dhunink/SaltScale/cad/exports/experimental/step/concept_v4_locator_fit_0p4_v1.step

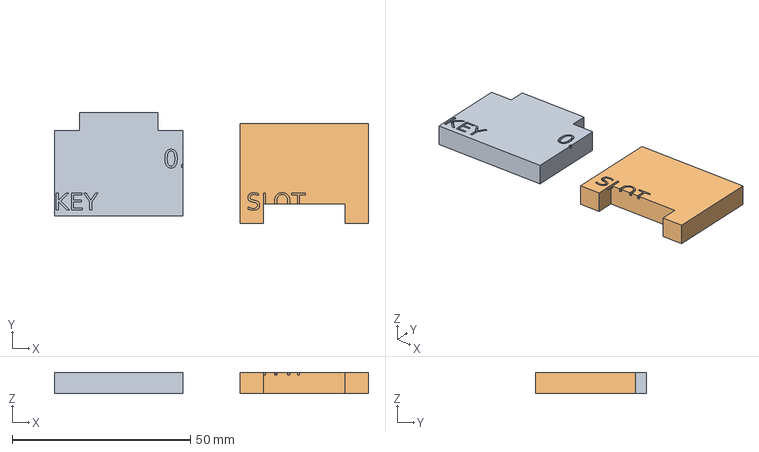
[picture p15: CAD file, 2026-06-13]
cad/exports/experimental/step/concept_v4_locator_fit_0p4_v1.step
88.0 x 31.0 x 6.00 mm
