dhunink/SaltScale/cad/exports/concept_v5_cartridge/step/concept_v5_round_load_puck.step

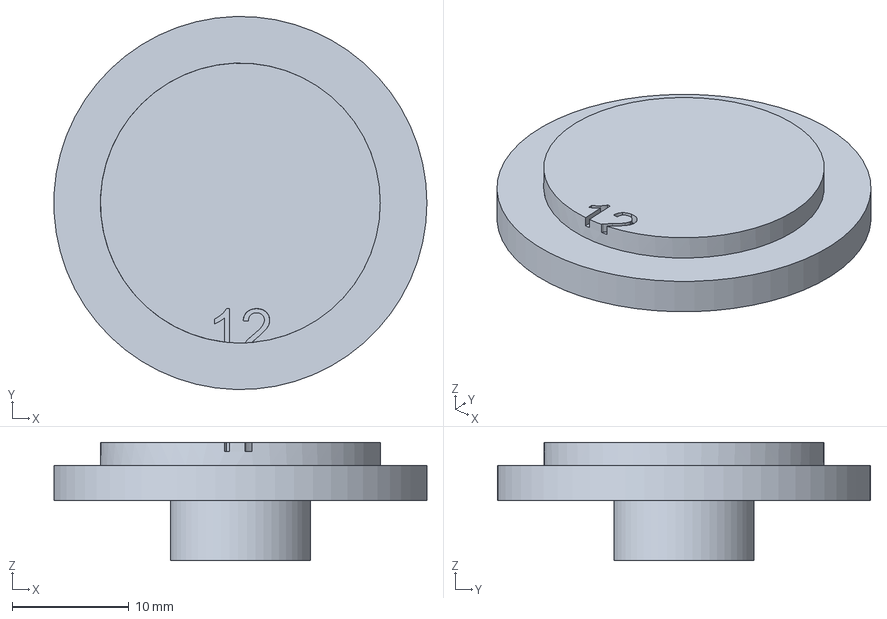
[picture p16: CAD file, 2026-06-15]
cad/exports/concept_v5_cartridge/step/concept_v5_round_load_puck.step
32.0 x 32.0 x 10.2 mm
