dhunink/SaltScale/cad/exports/experimental/step/concept_v4_lower_support_test_v1.step

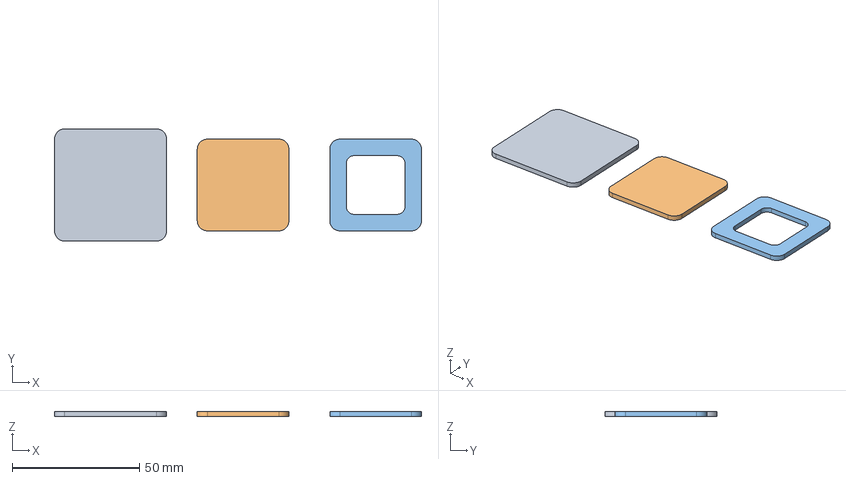
[picture p17: CAD file, 2026-06-13]
cad/exports/experimental/step/concept_v4_lower_support_test_v1.step
144.0 x 44.0 x 2.00 mm
