dhunink/SaltScale/cad/exports/rejected/step/concept_v4_upper_pad_carrier_pocket_test_v1.step

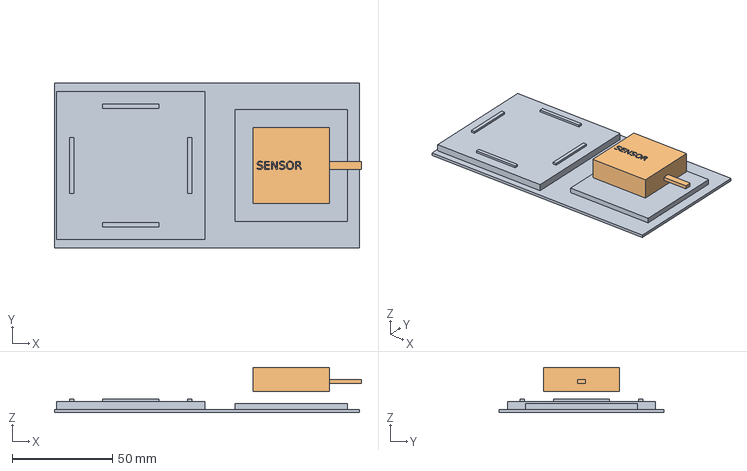
[picture p18: CAD file, 2026-06-13]
cad/exports/rejected/step/concept_v4_upper_pad_carrier_pocket_test_v1.step
153.0 x 82.0 x 22.6 mm
