dhunink/SaltScale/cad/exports/validated/step/concept_v4_upper_pad_pocket_round_cup_v1.step

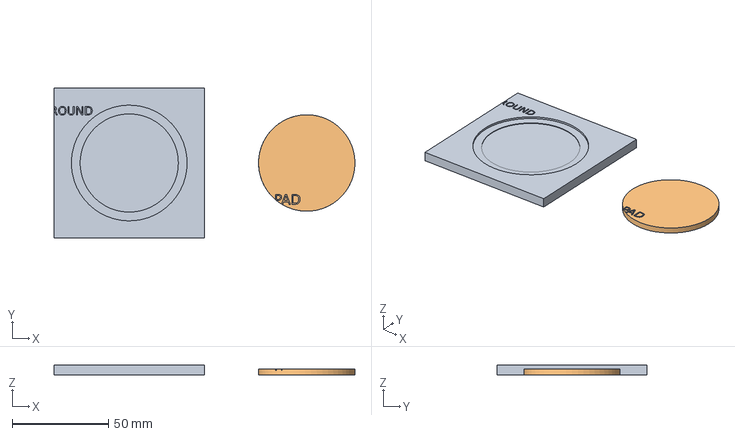
[picture p19: CAD file, 2026-06-13]
cad/exports/validated/step/concept_v4_upper_pad_pocket_round_cup_v1.step
156.0 x 78.0 x 5.00 mm
