dhunink/SaltScale/cad/exports/active/step/concept_v4_lower_pad.step

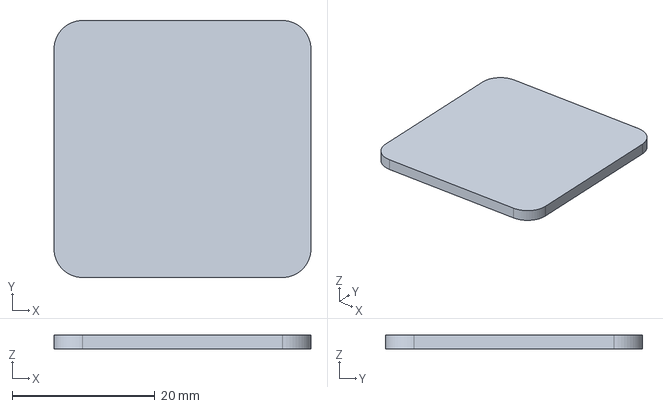
[picture p20: CAD file, 2026-06-13]
cad/exports/active/step/concept_v4_lower_pad.step
36.0 x 36.0 x 2.00 mm
