dhunink/SaltScale/cad/exports/concept_v5_cartridge/step/concept_v5_upper_segment_0.step

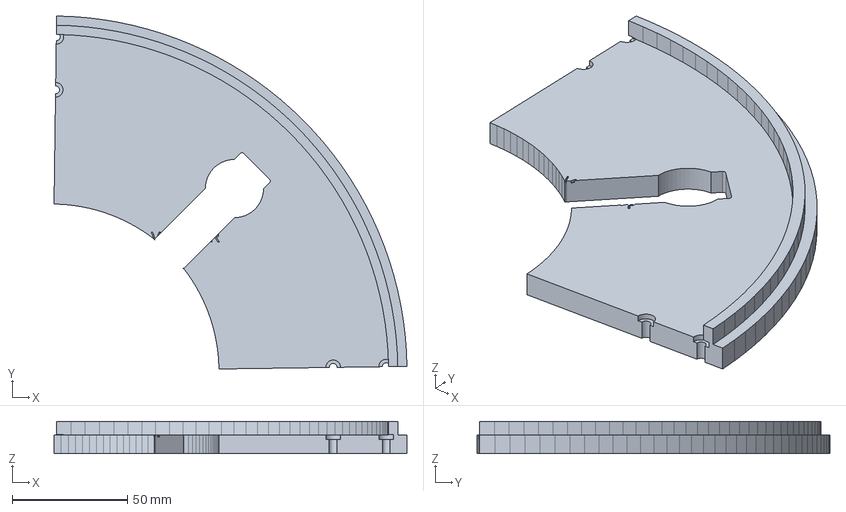
[picture p21: CAD file, 2026-06-15]
cad/exports/concept_v5_cartridge/step/concept_v5_upper_segment_0.step
153.0 x 153.0 x 14.0 mm
