dhunink/SaltScale/cad/exports/rejected/step/concept_v4_upper_pad_sensor_relative_test_v1.step

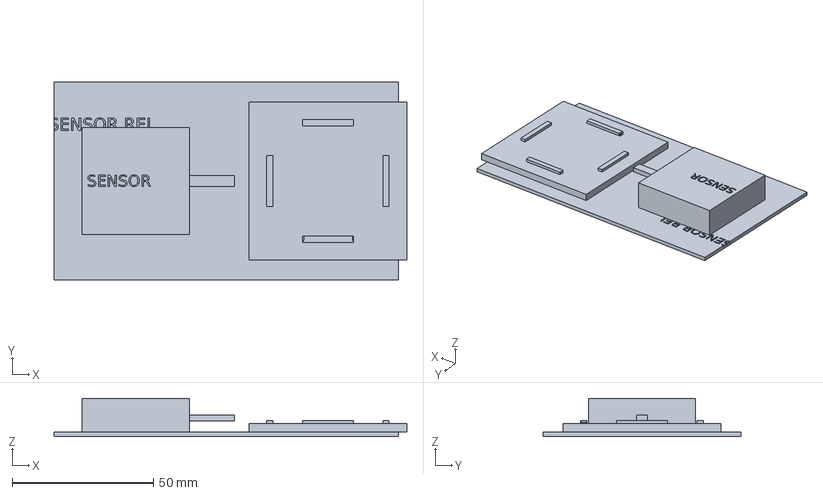
[picture p22: CAD file, 2026-06-13]
cad/exports/rejected/step/concept_v4_upper_pad_sensor_relative_test_v1.step
125.0 x 70.0 x 13.6 mm
