dhunink/SaltScale/cad/exports/active/step/concept_v4_sensor_placeholder.step

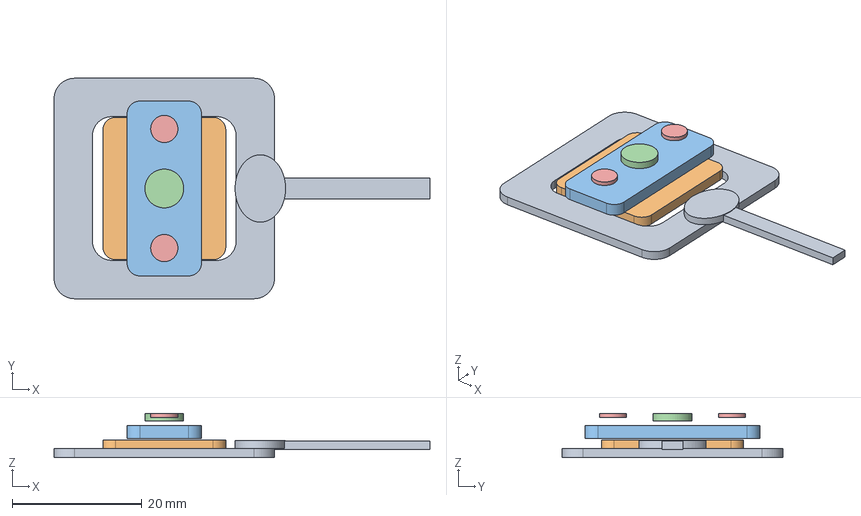
[picture p23: CAD file, 2026-06-13]
cad/exports/active/step/concept_v4_sensor_placeholder.step
58.1 x 34.1 x 6.84 mm
