dhunink/SaltScale/cad/exports/concept_v5_cartridge/step/concept_v5_lower_segment_0.step

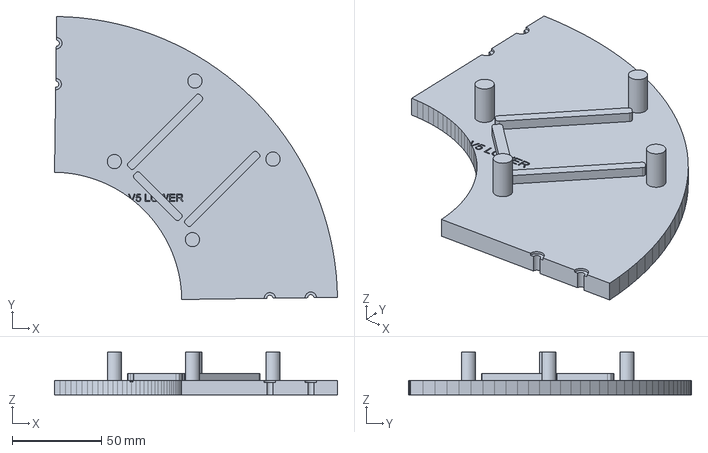
[picture p26: CAD file, 2026-06-15]
cad/exports/concept_v5_cartridge/step/concept_v5_lower_segment_0.step
159.0 x 159.0 x 24.0 mm
