dhunink/SaltScale/cad/exports/experimental/step/concept_v4_integrated_mini_seam_test_v1.step

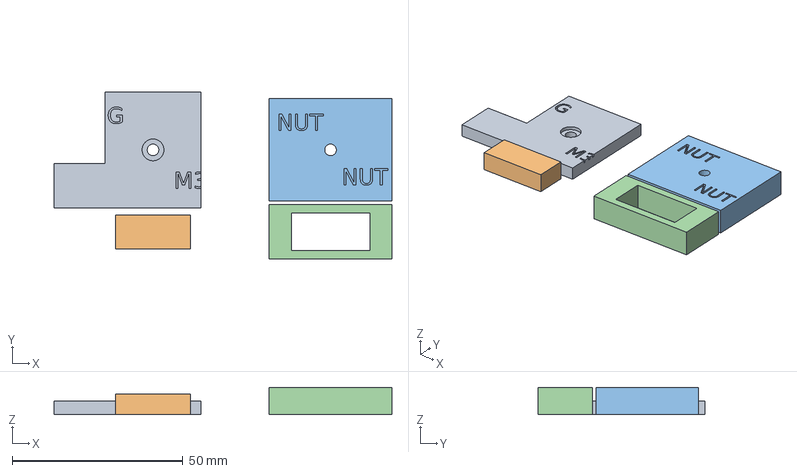
[picture p27: CAD file, 2026-06-13]
cad/exports/experimental/step/concept_v4_integrated_mini_seam_test_v1.step
99.0 x 49.0 x 8.00 mm
