dhunink/SaltScale/cad/exports/rejected/step/concept_v4_upper_pad_pocket_side_entry_v1.step

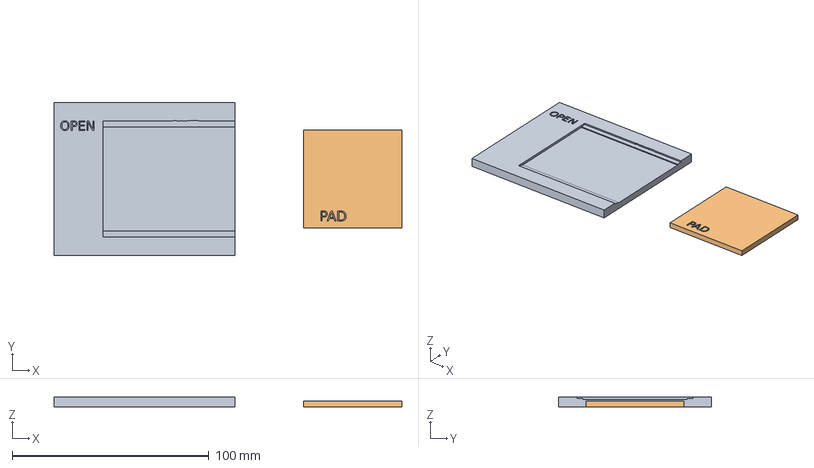
[picture p28: CAD file, 2026-06-13]
cad/exports/rejected/step/concept_v4_upper_pad_pocket_side_entry_v1.step
177.0 x 78.0 x 5.00 mm
