dhunink/SaltScale/cad/exports/concept_v5_cartridge/step/concept_v5_sensor_cartridge.step

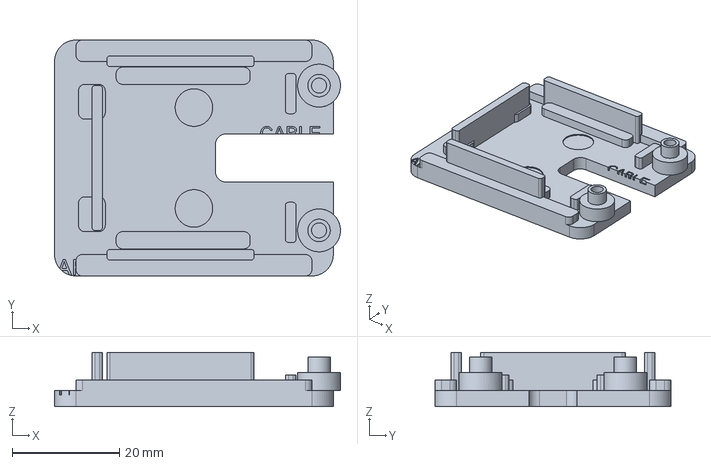
[picture p29: CAD file, 2026-06-15]
cad/exports/concept_v5_cartridge/step/concept_v5_sensor_cartridge.step
53.3 x 44.0 x 10.1 mm
