dhunink/SaltScale/cad/exports/experimental/step/printed_upper_seam_wedge_coupon_v2.step

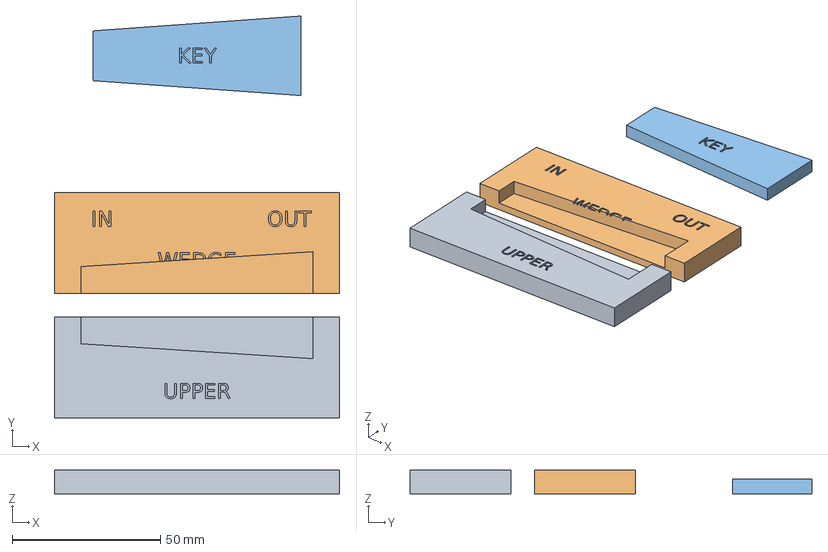
[picture p30: CAD file, 2026-06-13]
cad/exports/experimental/step/printed_upper_seam_wedge_coupon_v2.step
96.0 x 135.4 x 8.00 mm
