dhunink/SaltScale/cad/exports/validated/step/test_label_readability_v1.step

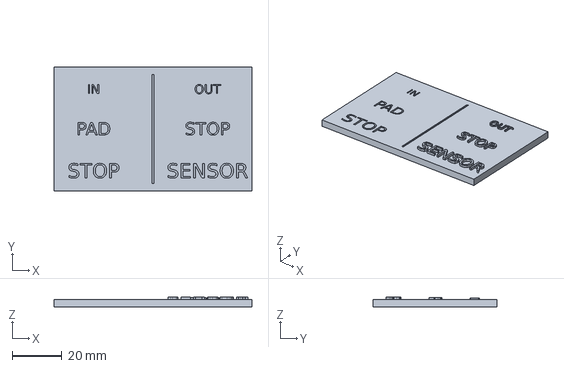
[picture p31: CAD file, 2026-06-13]
cad/exports/validated/step/test_label_readability_v1.step
80.0 x 50.0 x 4.00 mm
