dhunink/SaltScale/cad/exports/active/step/concept_v4_lower_segment_0.step

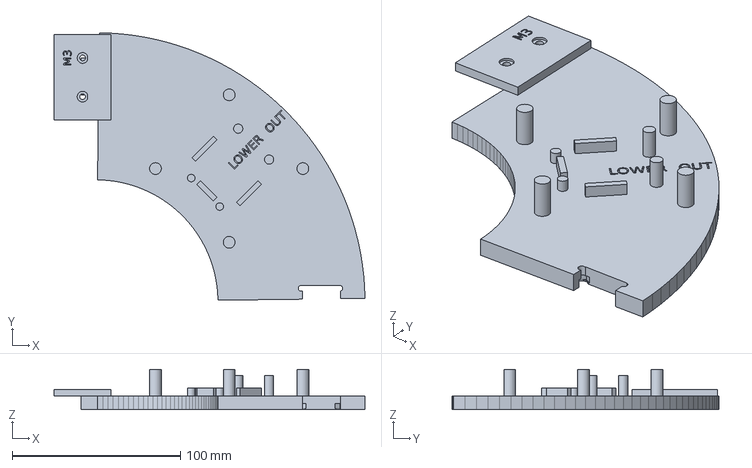
[picture p32: CAD file, 2026-06-13]
cad/exports/active/step/concept_v4_lower_segment_0.step
185.0 x 159.1 x 24.0 mm
