dhunink/SaltScale/cad/exports/concept_v5_cartridge/step/concept_v5_kiwi_sensor_reference.step

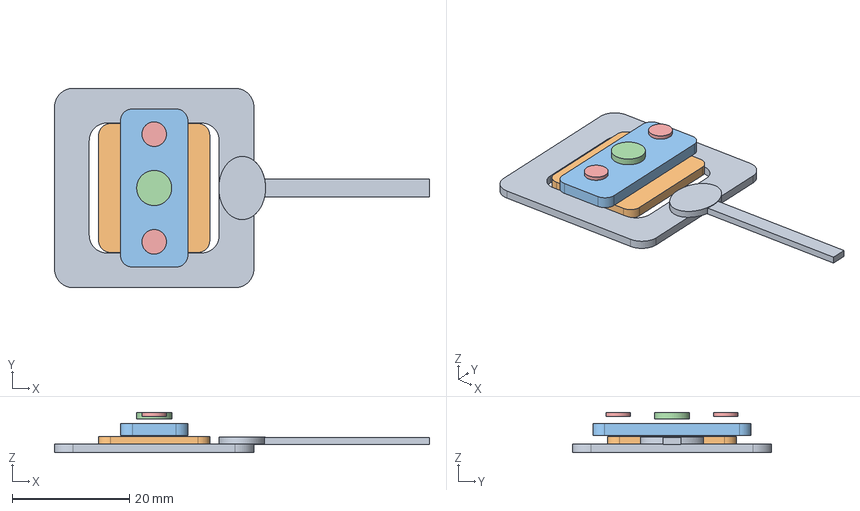
[picture p33: CAD file, 2026-06-15]
cad/exports/concept_v5_cartridge/step/concept_v5_kiwi_sensor_reference.step
64.1 x 34.1 x 6.84 mm
