dhunink/SaltScale/cad/exports/experimental/step/printed_upper_seam_sliding_key_coupon_v1.step

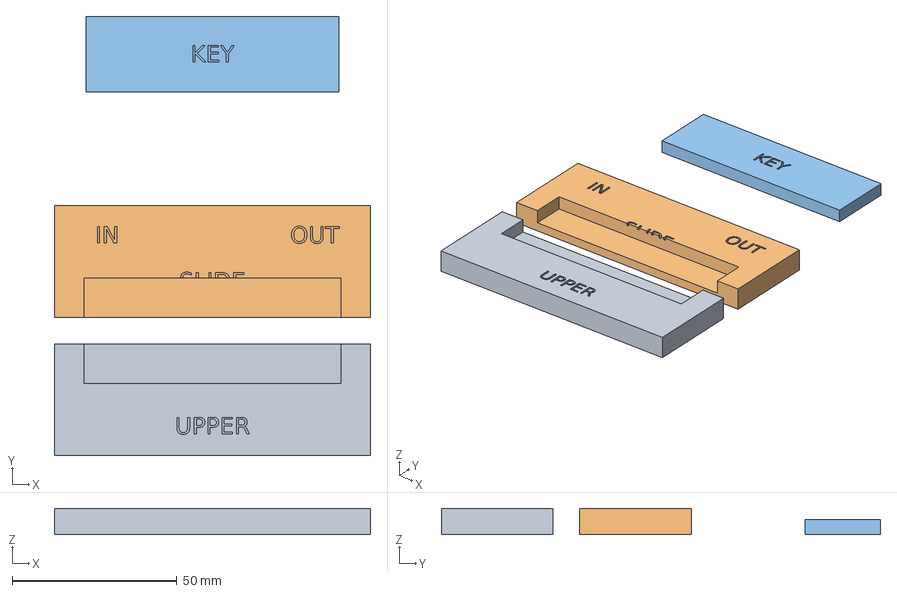
[picture p34: CAD file, 2026-06-13]
cad/exports/experimental/step/printed_upper_seam_sliding_key_coupon_v1.step
96.0 x 133.5 x 8.00 mm
