dhunink/SaltScale/cad/exports/validated/step/sensor_station_locator_v3.step

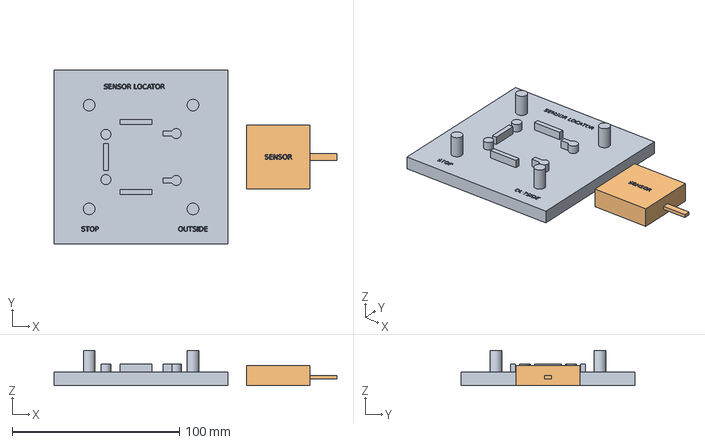
[picture p35: CAD file, 2026-06-13]
cad/exports/validated/step/sensor_station_locator_v3.step
169.0 x 104.0 x 21.0 mm
