dhunink/SaltScale/cad/exports/active/step/concept_v4_sensor_quarter_turn_clip.step

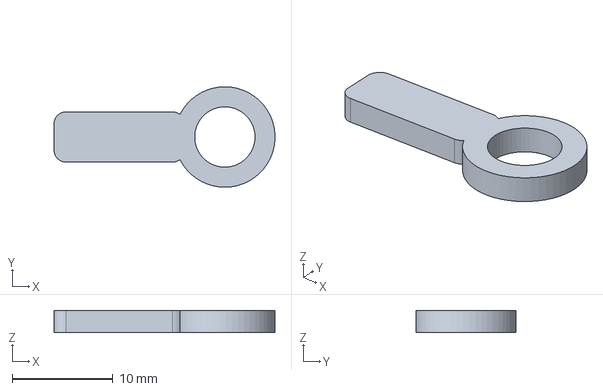
[picture p36: CAD file, 2026-06-13]
cad/exports/active/step/concept_v4_sensor_quarter_turn_clip.step
22.0 x 10.00 x 2.20 mm
