dhunink/SaltScale/cad/exports/validated/step/test_support_grate_fit_v1.step

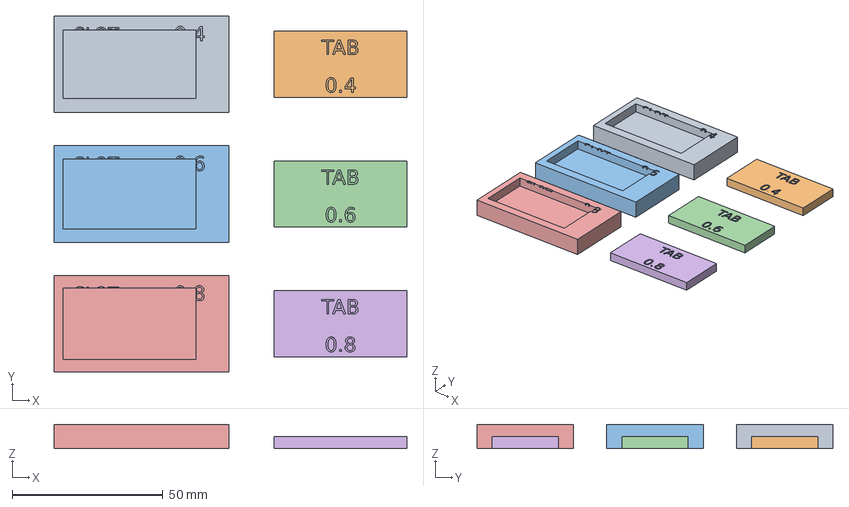
[picture p37: CAD file, 2026-06-13]
cad/exports/validated/step/test_support_grate_fit_v1.step
117.0 x 118.0 x 8.00 mm
