dhunink/SaltScale/cad/exports/experimental/step/concept_v4_real_sensor_locator_test_v2.step

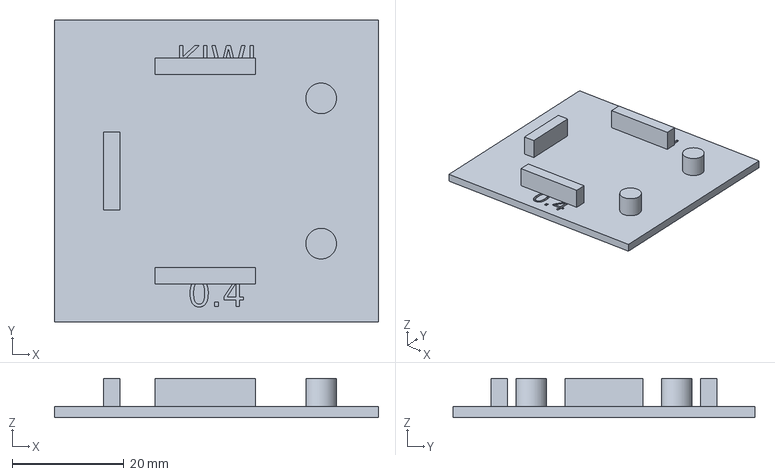
[picture p38: CAD file, 2026-06-13]
cad/exports/experimental/step/concept_v4_real_sensor_locator_test_v2.step
58.0 x 54.0 x 7.00 mm
