dhunink/SaltScale/cad/exports/validated/step/test_sensor_locator_v3_fit_v1.step

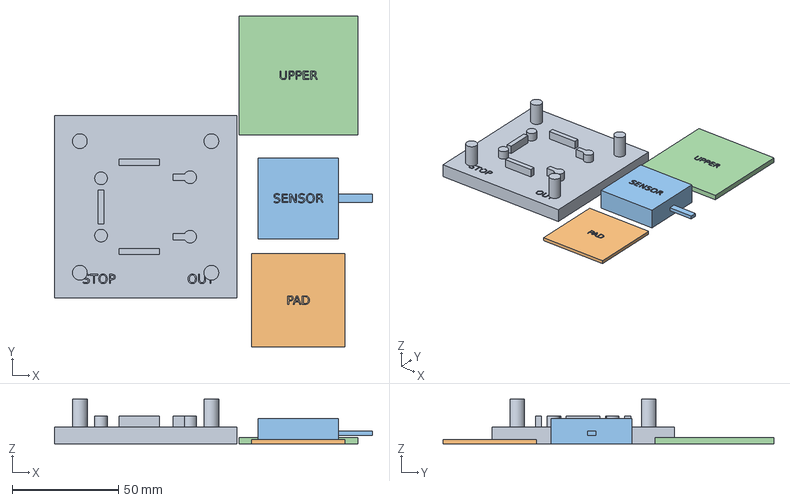
[picture p40: CAD file, 2026-06-13]
cad/exports/validated/step/test_sensor_locator_v3_fit_v1.step
150.0 x 156.0 x 21.0 mm
