dhunink/SaltScale/cad/exports/experimental/step/concept_v4_upper_lug_mating_block_v1.step

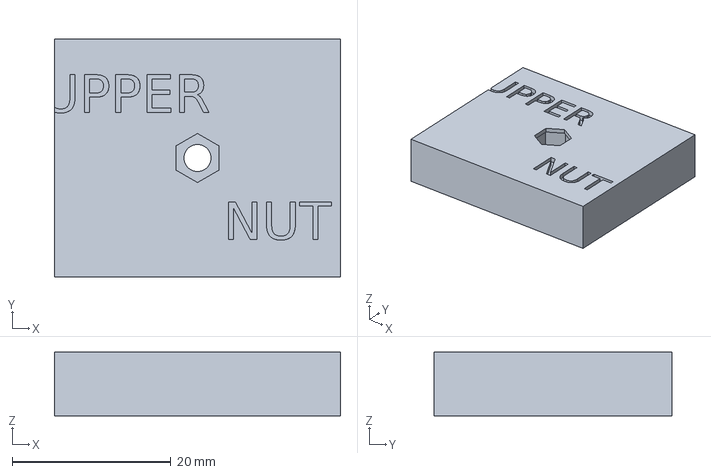
[picture p41: CAD file, 2026-06-13]
cad/exports/experimental/step/concept_v4_upper_lug_mating_block_v1.step
36.0 x 30.0 x 8.00 mm
