dhunink/SaltScale/cad/exports/experimental/step/concept_v4_sensor_clip_station_coupon_v1.step

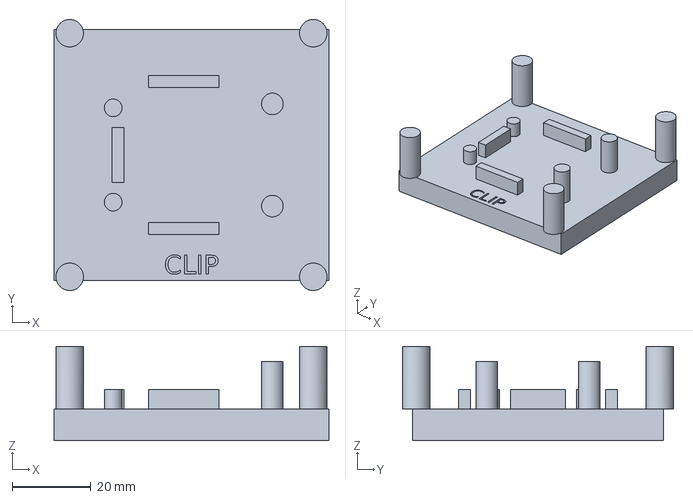
[picture p42: CAD file, 2026-06-13]
cad/exports/experimental/step/concept_v4_sensor_clip_station_coupon_v1.step
70.0 x 69.0 x 24.0 mm
