dhunink/SaltScale/cad/exports/experimental/step/concept_v4_sensor_clip_station_open_closed.step

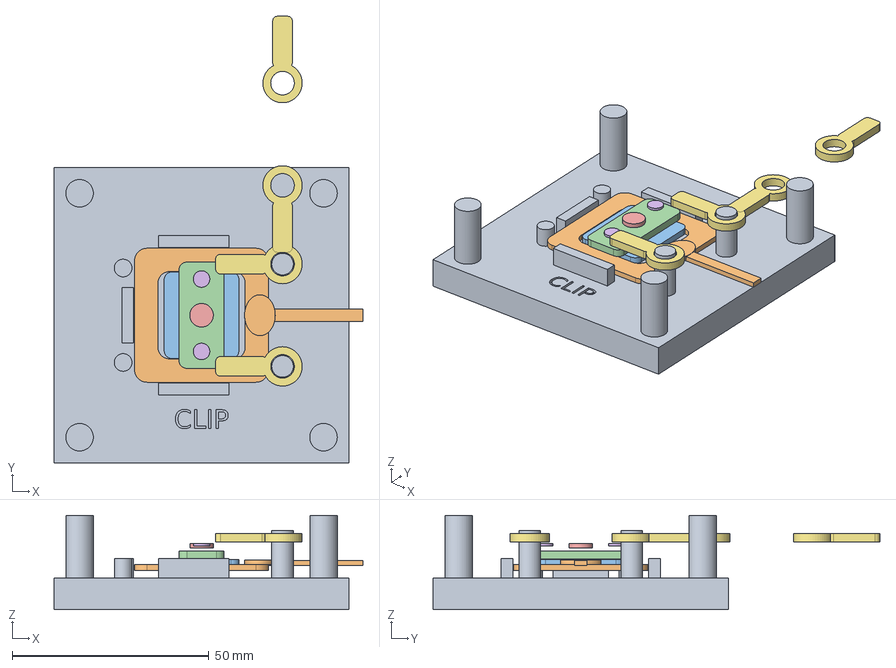
[picture p43: CAD file, 2026-06-13]
cad/exports/experimental/step/concept_v4_sensor_clip_station_open_closed.step
78.5 x 113.5 x 24.0 mm
sensor_station_coupon_body_part
kiwi_sensor_reference_part
sensor_0_front_clip_top_closed_part
sensor_0_front_clip_bottom_closed_part
sensor_0_front_clip_top_open_part
sensor_0_front_clip_bottom_open_part
