dhunink/SaltScale/cad/exports/experimental/step/concept_v4_sensor_clip_station_coupon_v2.step

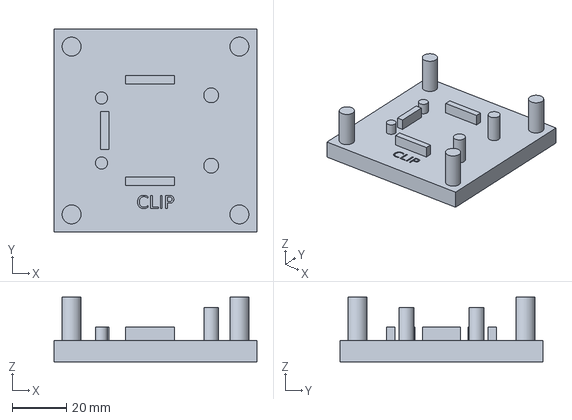
[picture p44: CAD file, 2026-06-13]
cad/exports/experimental/step/concept_v4_sensor_clip_station_coupon_v2.step
75.0 x 75.0 x 24.0 mm
