dhunink/SaltScale/cad/exports/experimental/step/concept_v4_upper_lug_recess_block_v1.step

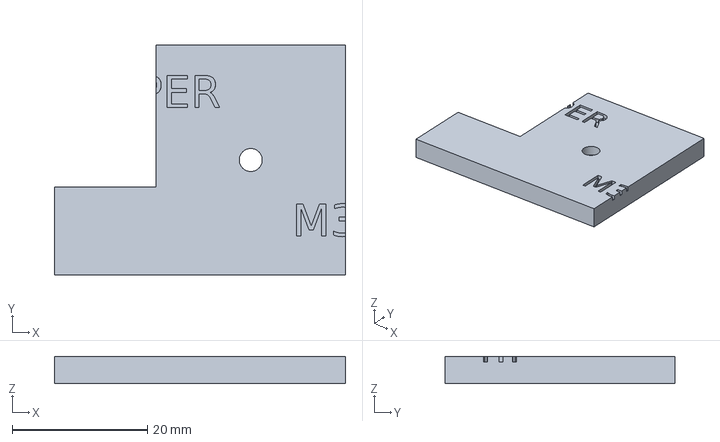
[picture p45: CAD file, 2026-06-13]
cad/exports/experimental/step/concept_v4_upper_lug_recess_block_v1.step
43.0 x 34.0 x 4.00 mm
