dhunink/SaltScale/cad/exports/experimental/step/printed_upper_seam_true_dovetail_coupon_v1.step

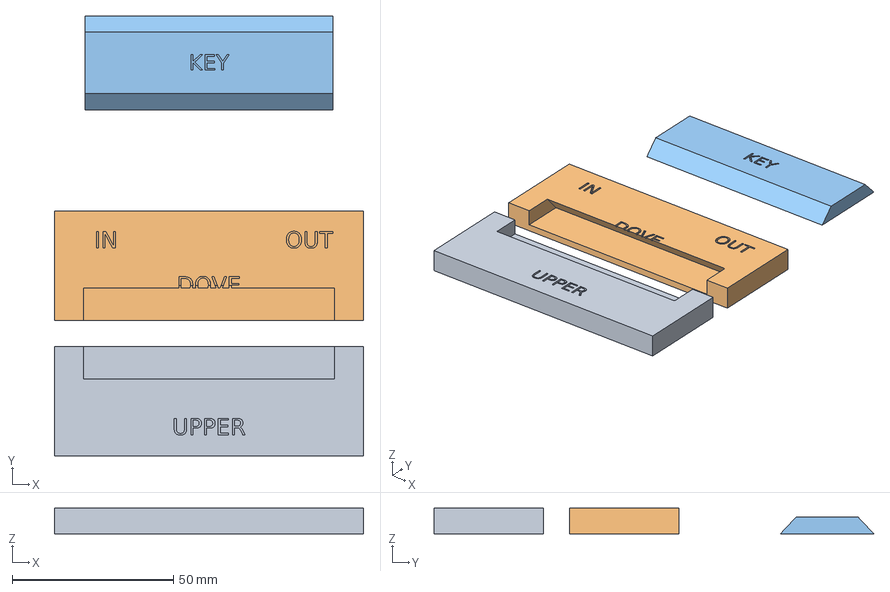
[picture p46: CAD file, 2026-06-13]
cad/exports/experimental/step/printed_upper_seam_true_dovetail_coupon_v1.step
96.0 x 136.6 x 8.00 mm
