dhunink/SaltScale/cad/exports/experimental/step/concept_v4_lower_integrated_seam_coupon_v1.step

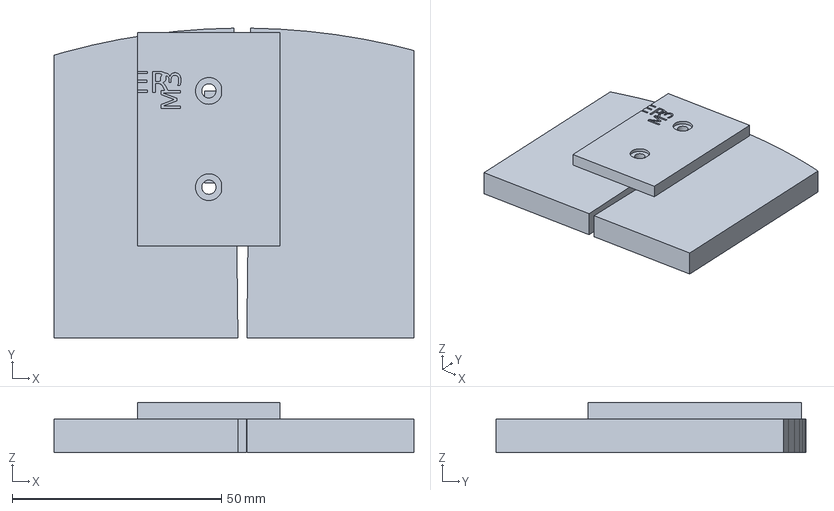
[picture p47: CAD file, 2026-06-13]
cad/exports/experimental/step/concept_v4_lower_integrated_seam_coupon_v1.step
86.0 x 74.0 x 12.0 mm
